KweBoakye/dactyl-manuform-mini-keyboard/parts/caps/DES-kyria-R1T1.stl

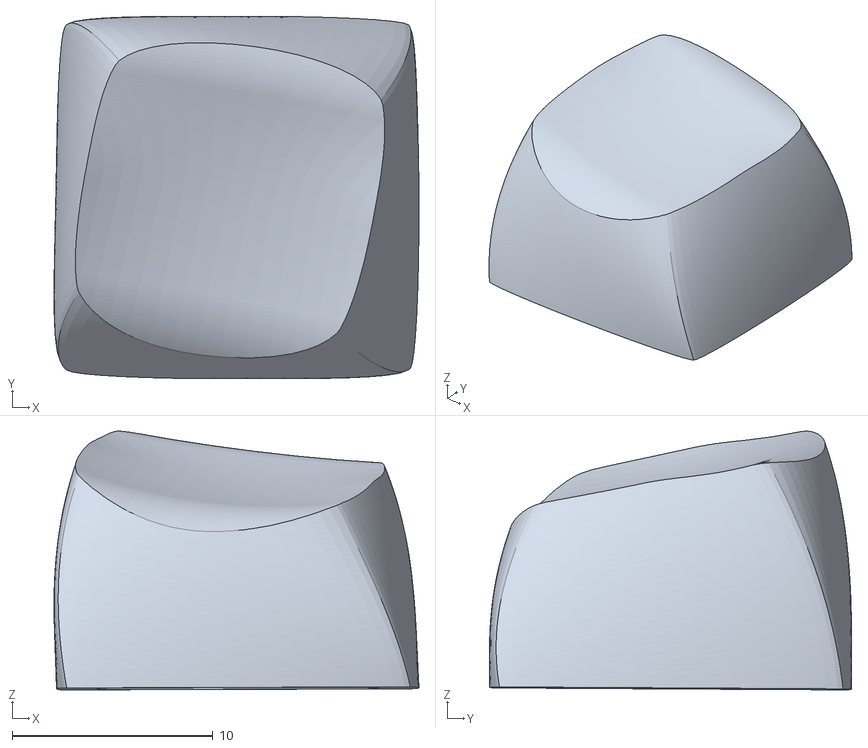
[picture p18: CAD file, 2022-10-28]
parts/caps/DES-kyria-R1T1.stl
18.2 x 18.1 x 12.9
