KweBoakye/dactyl-manuform-mini-keyboard/parts/caps/DES-R4.stl

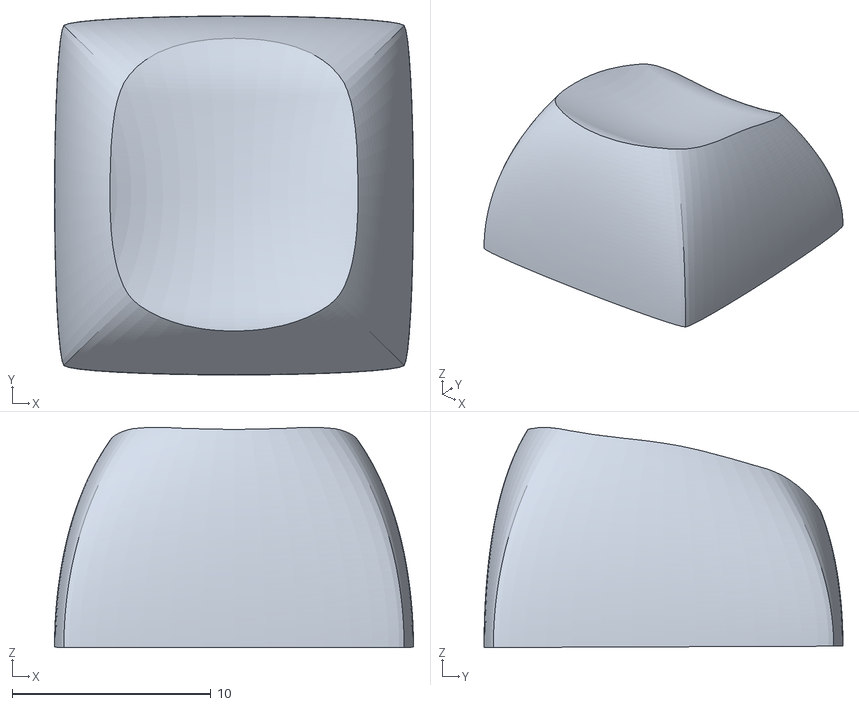
[picture p19: CAD file, 2022-10-28]
parts/caps/DES-R4.stl
18.1 x 18.1 x 11.1
