KweBoakye/dactyl-manuform-mini-keyboard/parts/plate_v4_103.stl

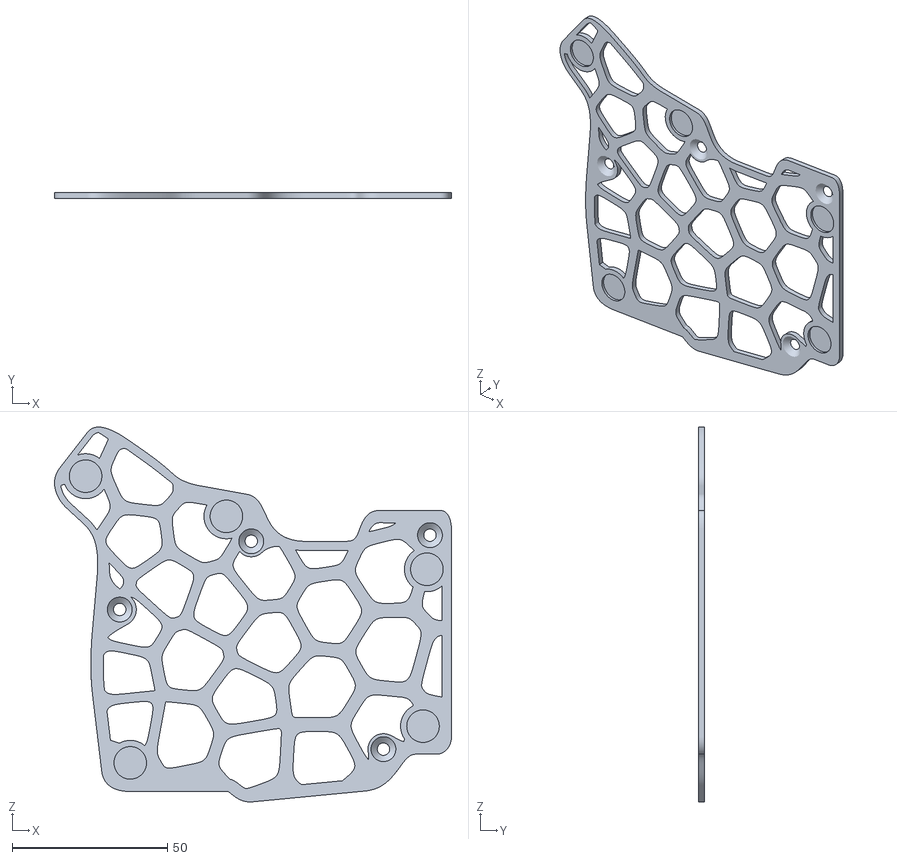
[picture p20: CAD file, 2024-05-14]
parts/plate_v4_103.stl
128.0 x 2.00 x 120.9
