KweBoakye/dactyl-manuform-mini-keyboard/parts/caps/DES-R5.stl

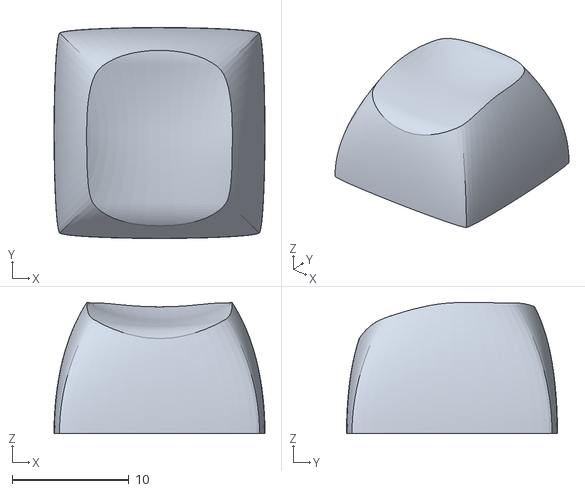
[picture p21: CAD file, 2022-10-28]
parts/caps/DES-R5.stl
18.1 x 18.1 x 11.2
