KweBoakye/dactyl-manuform-mini-keyboard/parts/ImageToStl.com_dt_azc276a02_pcb1_00a.stl

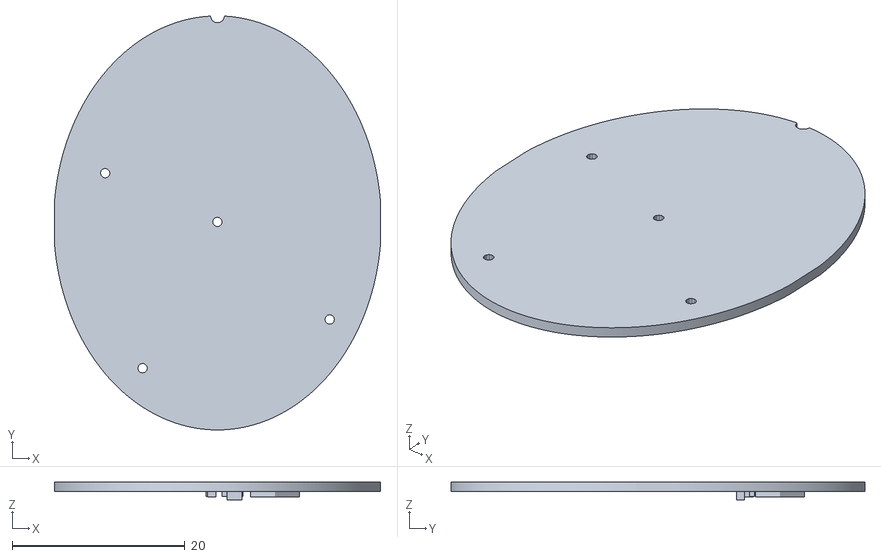
[picture p22: CAD file, 2024-05-14]
parts/ImageToStl.com_dt_azc276a02_pcb1_00a.stl
37.8 x 48.0 x 2.04
