KweBoakye/dactyl-manuform-mini-keyboard/parts/caps/DES-kyria-R1T0.stl

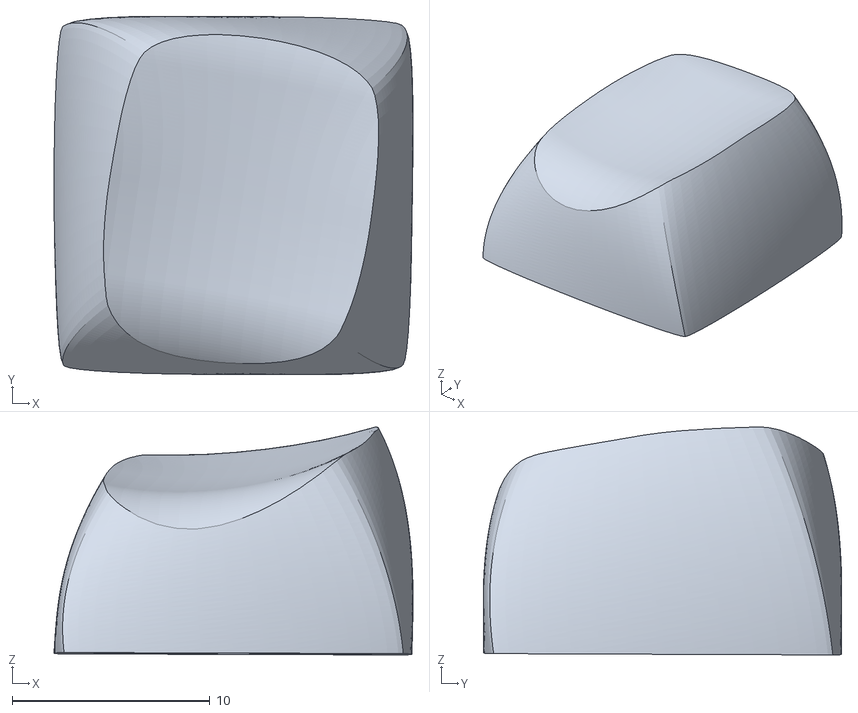
[picture p23: CAD file, 2022-10-28]
parts/caps/DES-kyria-R1T0.stl
18.1 x 18.1 x 11.5
