KweBoakye/dactyl-manuform-mini-keyboard/parts/crkbd-baseplate-magsafe.stl

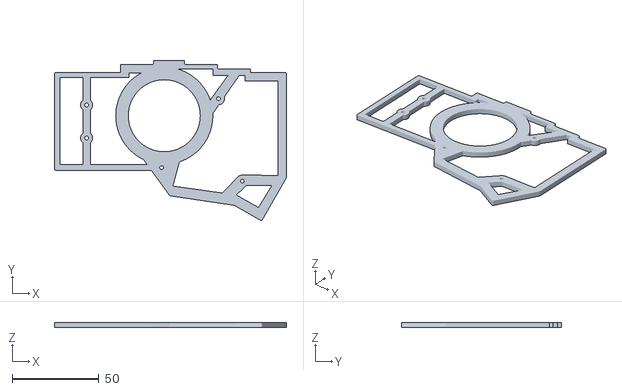
[picture p24: CAD file, 2024-05-14]
parts/crkbd-baseplate-magsafe.stl
133.8 x 92.2 x 3.00
