KweBoakye/dactyl-manuform-mini-keyboard/parts/caps/DES-R3.stl

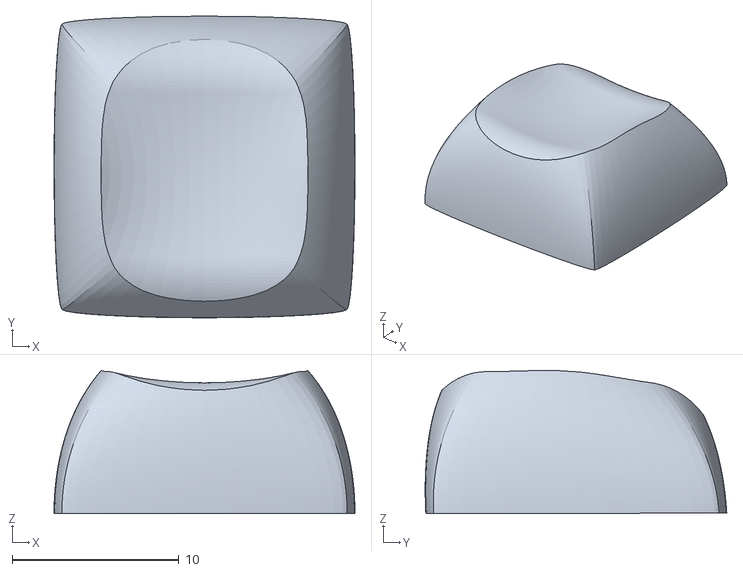
[picture p25: CAD file, 2022-10-28]
parts/caps/DES-R3.stl
18.1 x 18.1 x 8.60
