KweBoakye/dactyl-manuform-mini-keyboard/parts/spi_eeprom_breakout.stl

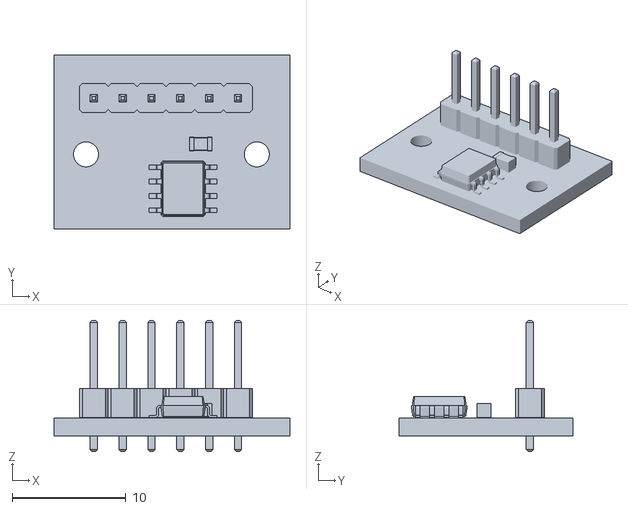
[picture p26: CAD file, 2023-10-07]
parts/spi_eeprom_breakout.stl
20.8 x 15.3 x 11.5
