KweBoakye/dactyl-manuform-mini-keyboard/parts/caps/DES-R2.stl

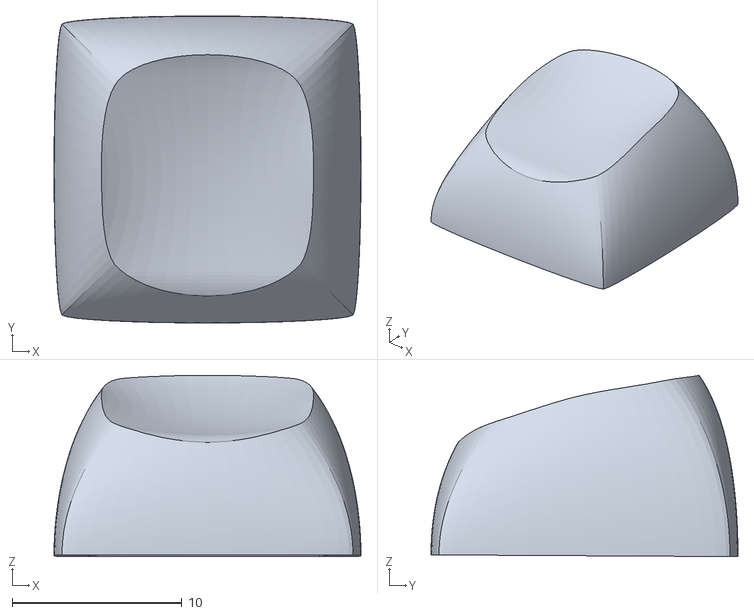
[picture p27: CAD file, 2022-10-28]
parts/caps/DES-R2.stl
18.1 x 18.1 x 10.7
