KweBoakye/dactyl-manuform-mini-keyboard/parts/Tps-65-breakout.stl

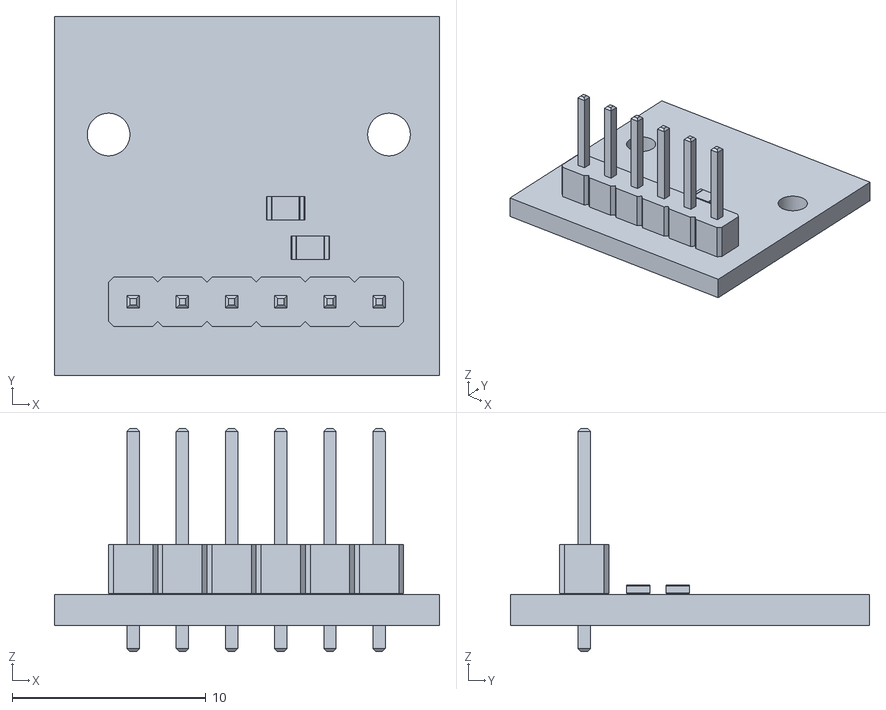
[picture p28: CAD file, 2023-10-07]
parts/Tps-65-breakout.stl
19.9 x 18.5 x 11.5
