KweBoakye/dactyl-manuform-mini-keyboard/parts/caps/DES-R1.stl

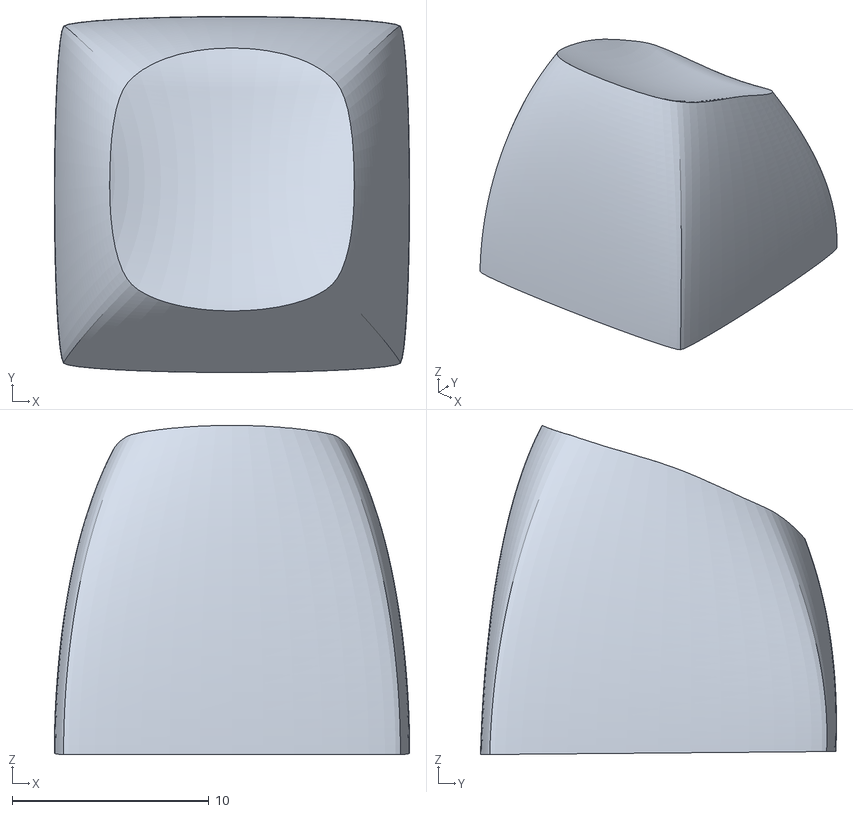
[picture p29: CAD file, 2022-10-28]
parts/caps/DES-R1.stl
18.1 x 18.1 x 16.7
