KweBoakye/dactyl-manuform-mini-keyboard/parts/sk8707-5x-breakout.stl

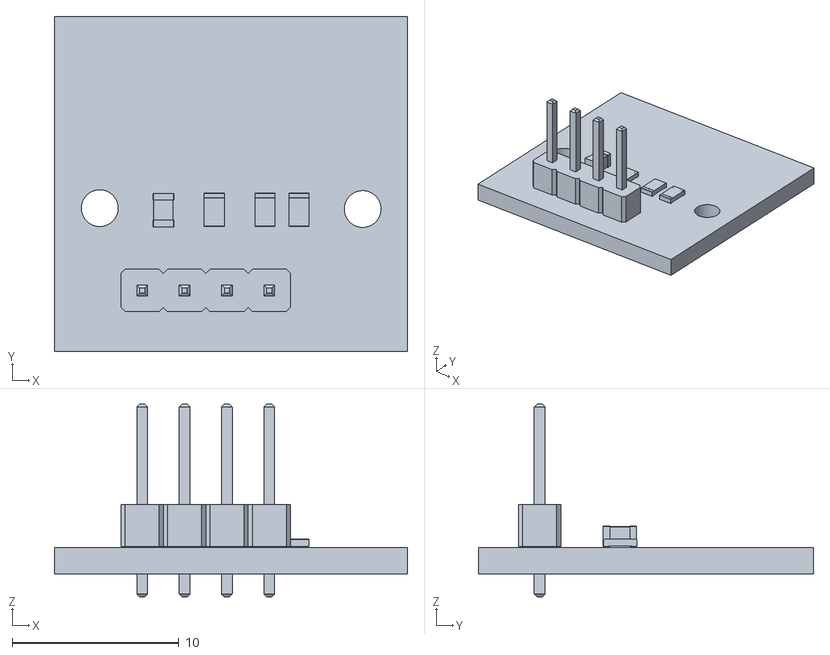
[picture p30: CAD file, 2023-10-07]
parts/sk8707-5x-breakout.stl
21.2 x 20.1 x 11.5
