KweBoakye/dactyl-manuform-mini-keyboard/parts/caps/DES-kyria-R1T3.stl

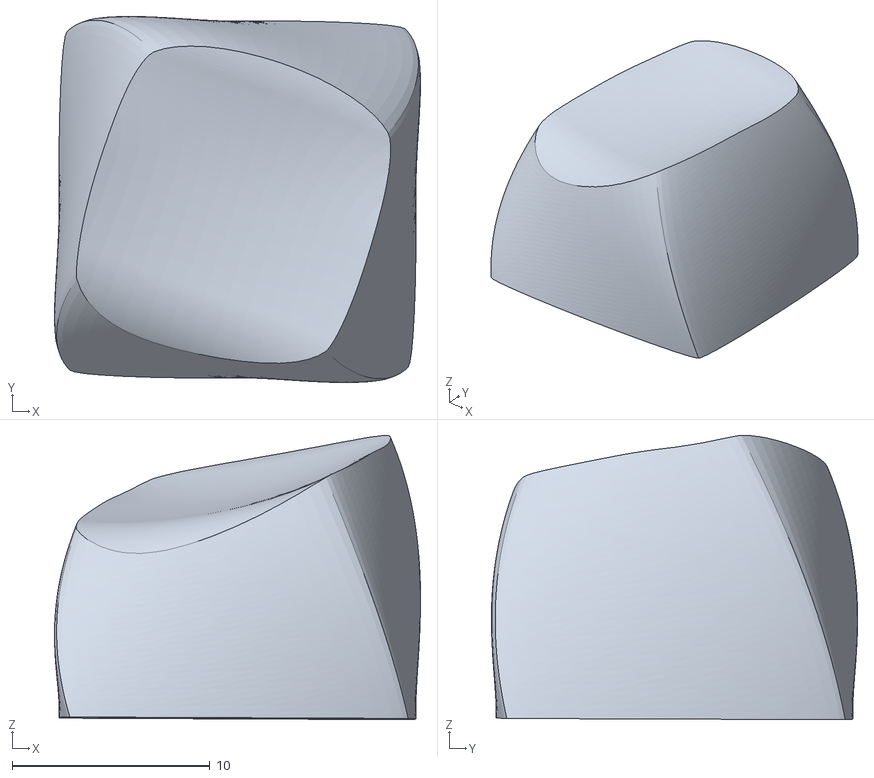
[picture p31: CAD file, 2022-10-28]
parts/caps/DES-kyria-R1T3.stl
18.5 x 18.5 x 14.4
