KweBoakye/dactyl-manuform-mini-keyboard/parts/IS31FL3743x_Breakout.stl

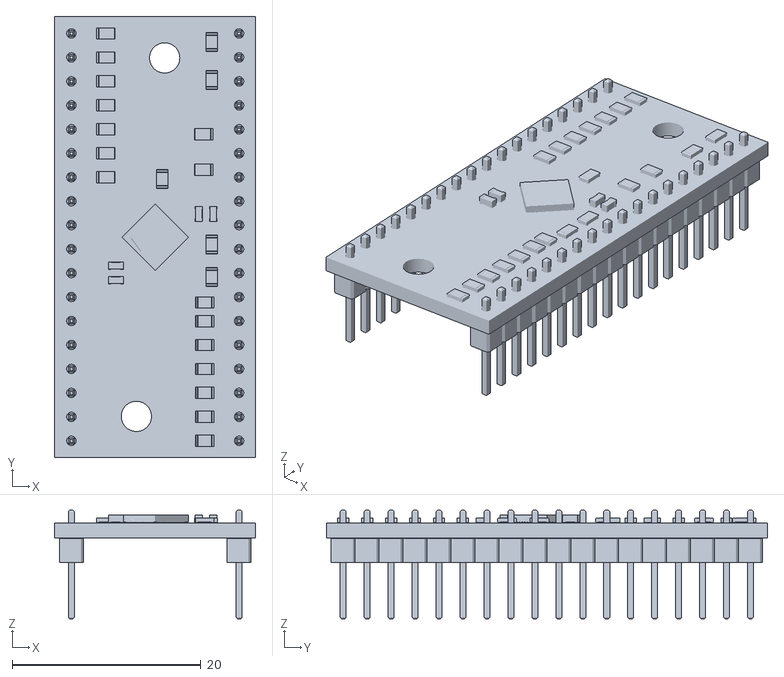
[picture p32: CAD file, 2023-10-07]
parts/IS31FL3743x_Breakout.stl
21.3 x 46.8 x 11.5
