KweBoakye/dactyl-manuform-mini-keyboard/parts/2305 DRV2605L.stl

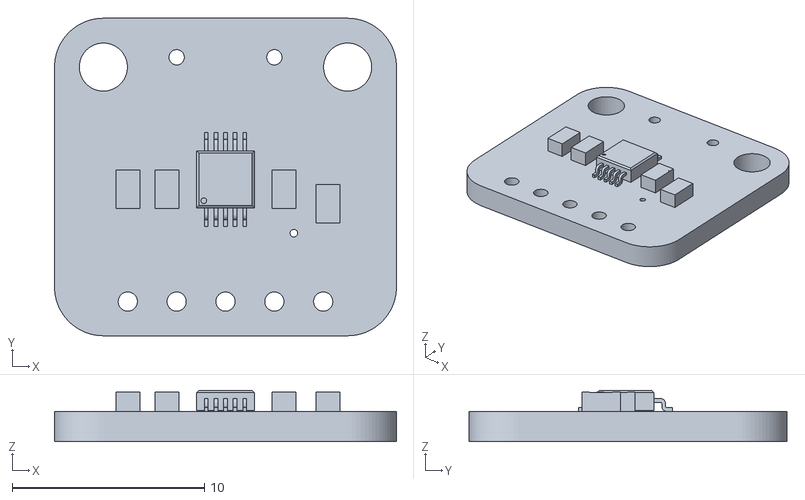
[picture p33: CAD file, 2023-10-07]
parts/2305 DRV2605L.stl
17.8 x 16.5 x 2.67
