KweBoakye/dactyl-manuform-mini-keyboard/parts/tps-43.stl

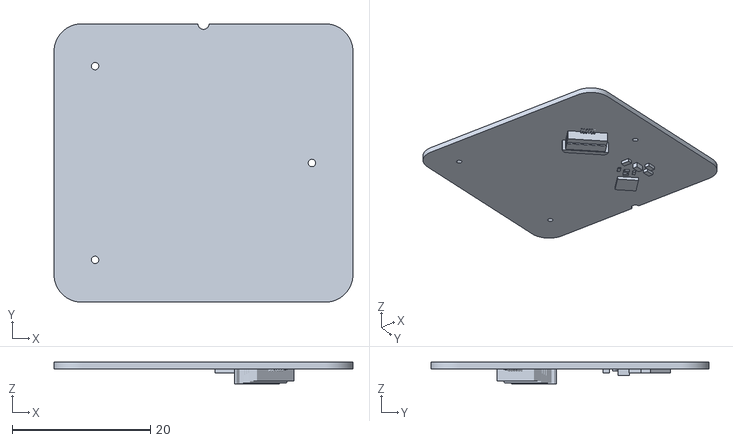
[picture p34: CAD file, 2023-08-23]
parts/tps-43.stl
43.3 x 40.3 x 3.15
