KweBoakye/dactyl-manuform-mini-keyboard/parts/tps-65.stl

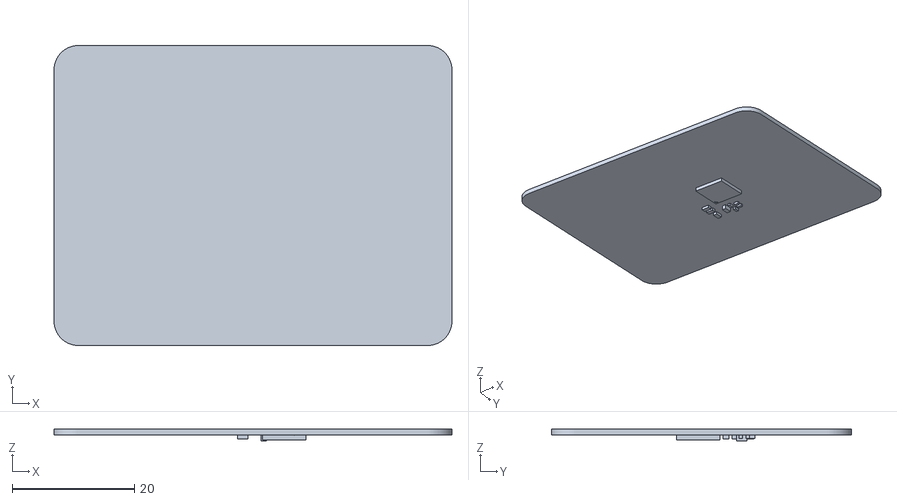
[picture p35: CAD file, 2023-08-23]
parts/tps-65.stl
65.0 x 49.0 x 1.95
