KweBoakye/dactyl-manuform-mini-keyboard/parts/pin header  2.54-12.stl

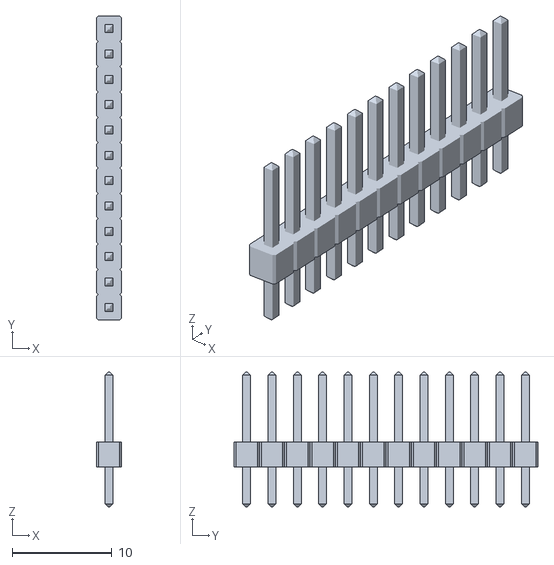
[picture p36: CAD file, 2023-05-24]
parts/pin header 2.54-12.stl
2.54 x 30.5 x 13.5
