KweBoakye/dactyl-manuform-mini-keyboard/parts/adafruit kb2040.stl

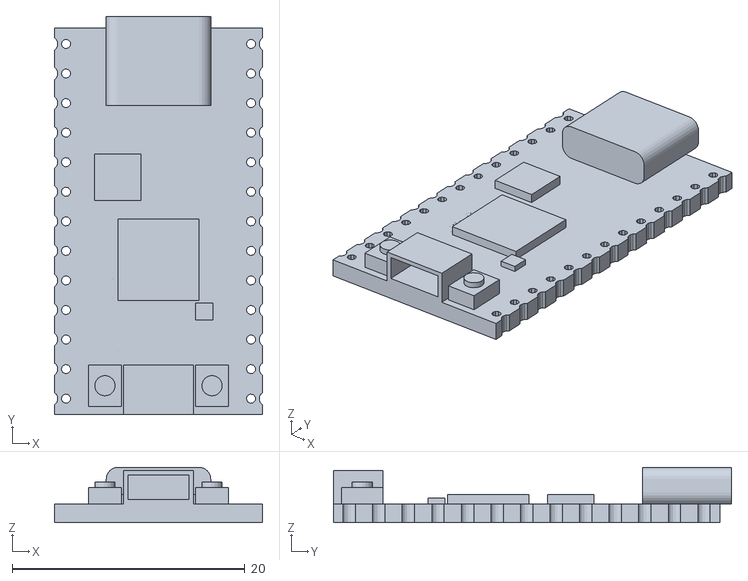
[picture p37: CAD file, 2023-05-24]
parts/adafruit kb2040.stl
17.9 x 34.2 x 4.75
