KweBoakye/dactyl-manuform-mini-keyboard/parts/pim452.stl

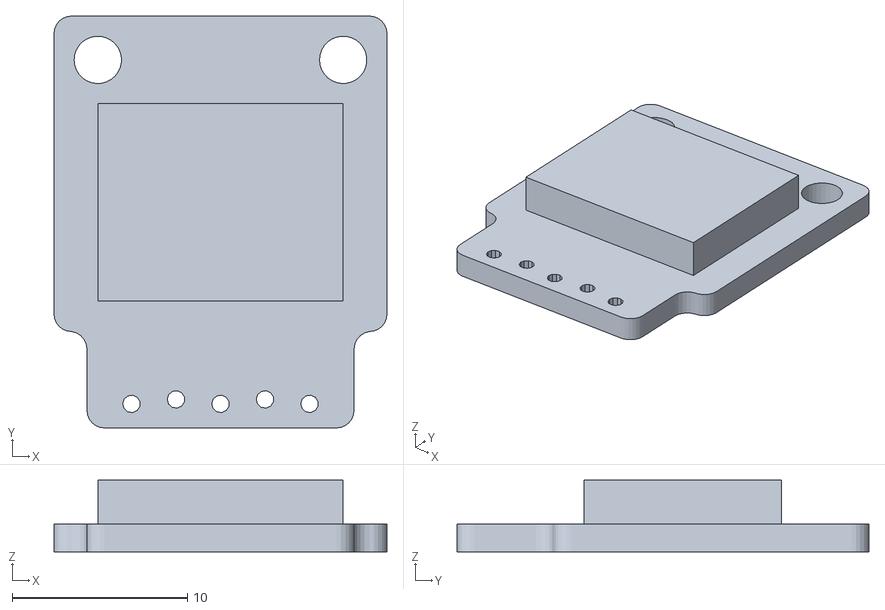
[picture p38: CAD file, 2023-05-24]
parts/pim452.stl
19.0 x 23.5 x 4.10
