KweBoakye/dactyl-manuform-mini-keyboard/parts/pico-r3.stl

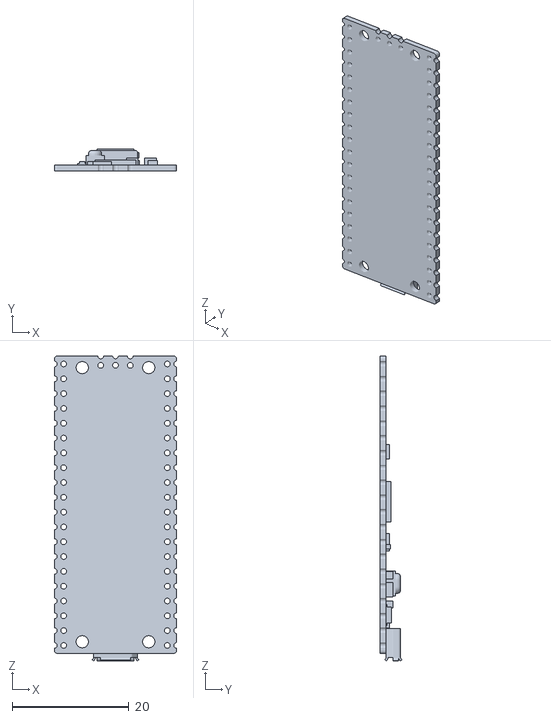
[picture p39: CAD file, 2023-05-17]
parts/pico-r3.stl
21.0 x 3.73 x 52.3
