KweBoakye/dactyl-manuform-mini-keyboard/parts/USB_Type_C_Female_Connector.stl

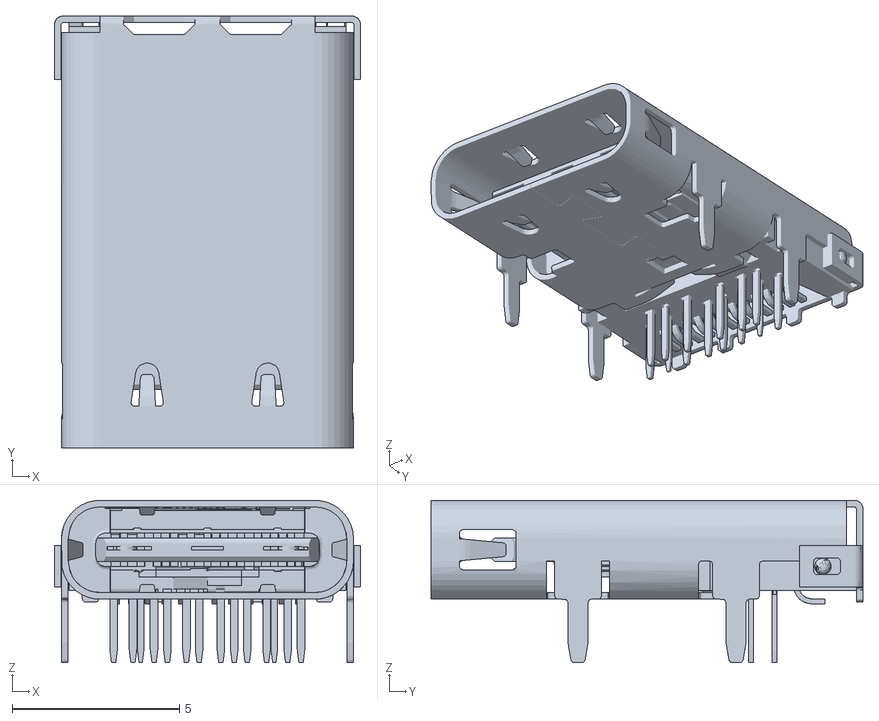
[picture p40: CAD file, 2023-05-17]
parts/USB_Type_C_Female_Connector.stl
9.16 x 12.9 x 4.86
