KweBoakye/dactyl-manuform-mini-keyboard/parts/Kailh LP Choc Burnt Orange.stl

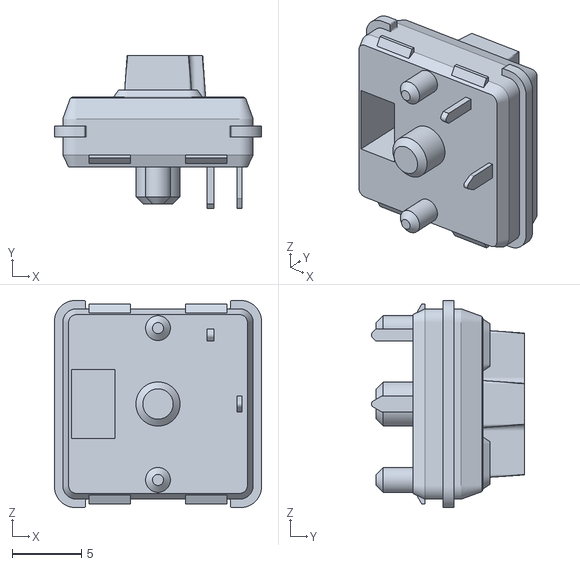
[picture p41: CAD file, 2023-05-17]
parts/Kailh LP Choc Burnt Orange.stl
15.0 x 11.1 x 15.0
