KweBoakye/dactyl-manuform-mini-keyboard/parts/usb connector type c female 6pin.stl

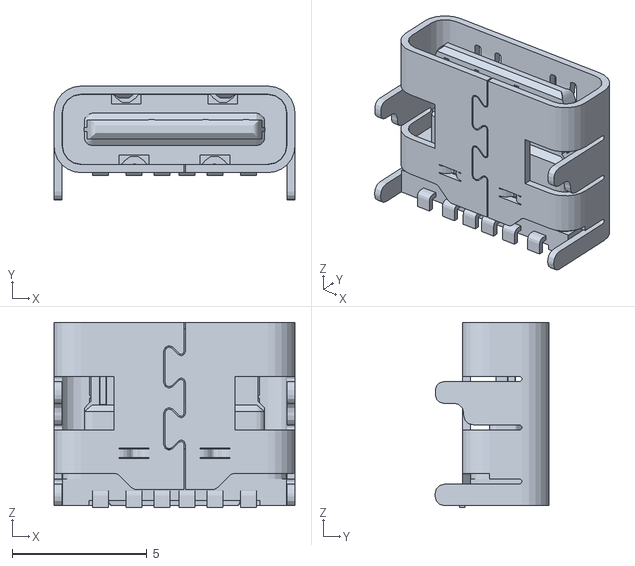
[picture p42: CAD file, 2023-05-17]
parts/usb connector type c female 6pin.stl
8.94 x 4.22 x 6.87
