KweBoakye/dactyl-manuform-mini-keyboard/parts/KLOR_polydactyl_3DP_switchplate.stl

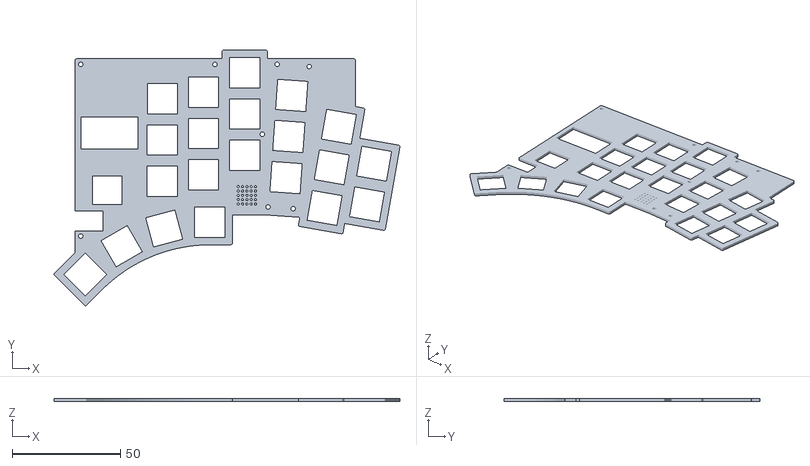
[picture p43: CAD file, 2023-03-25]
parts/KLOR_polydactyl_3DP_switchplate.stl
160.0 x 118.2 x 1.50
