KweBoakye/dactyl-manuform-mini-keyboard/parts/2.54mm x 1 Male Header.stl

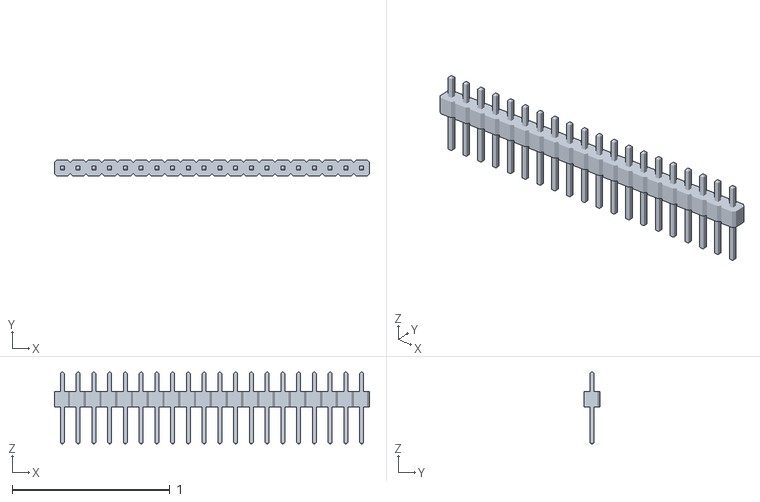
[picture p44: CAD file, 2022-12-14]
parts/2.54mm x 1 Male Header.stl
2.00 x 0.1 x 0.454
