KweBoakye/dactyl-manuform-mini-keyboard/parts/ImageToStl.com_pin header 1x16 th pitch 2.54mm.stl

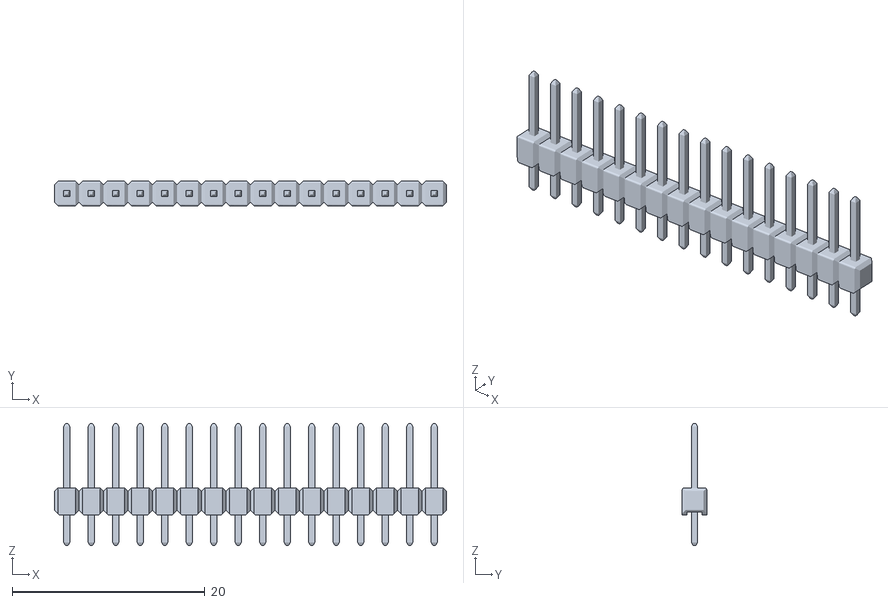
[picture p45: CAD file, 2022-12-14]
parts/ImageToStl.com_pin header 1x16 th pitch 2.54mm.stl
40.6 x 2.54 x 12.7
