KweBoakye/dactyl-manuform-mini-keyboard/parts/Kailh Polia.stl

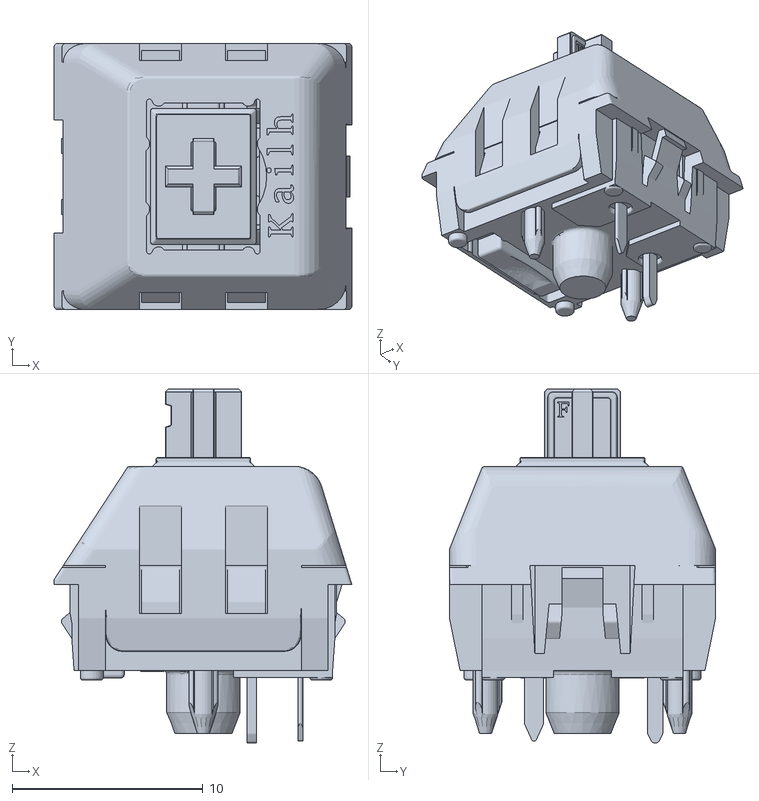
[picture p46: CAD file, 2022-10-28]
parts/Kailh Polia.stl
15.6 x 13.9 x 18.5
