KweBoakye/dactyl-manuform-mini-keyboard/parts/ST7789.stl

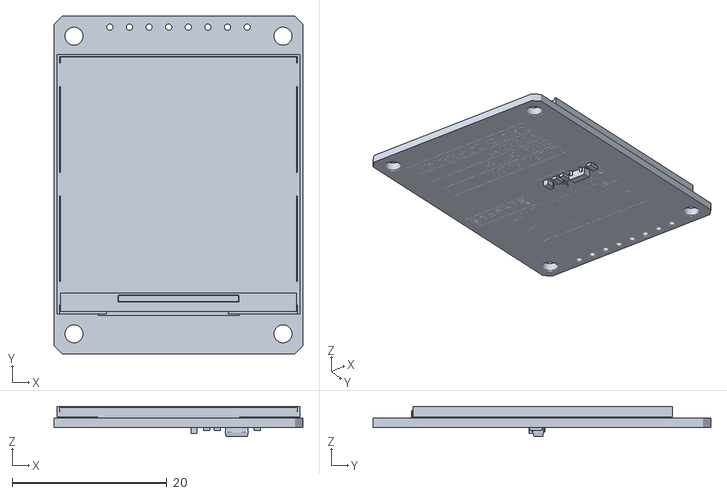
[picture p47: CAD file, 2022-10-28]
parts/ST7789.stl
32.2 x 43.7 x 3.89
