KweBoakye/dactyl-manuform-mini-keyboard/parts/tactileswitch-short.STL

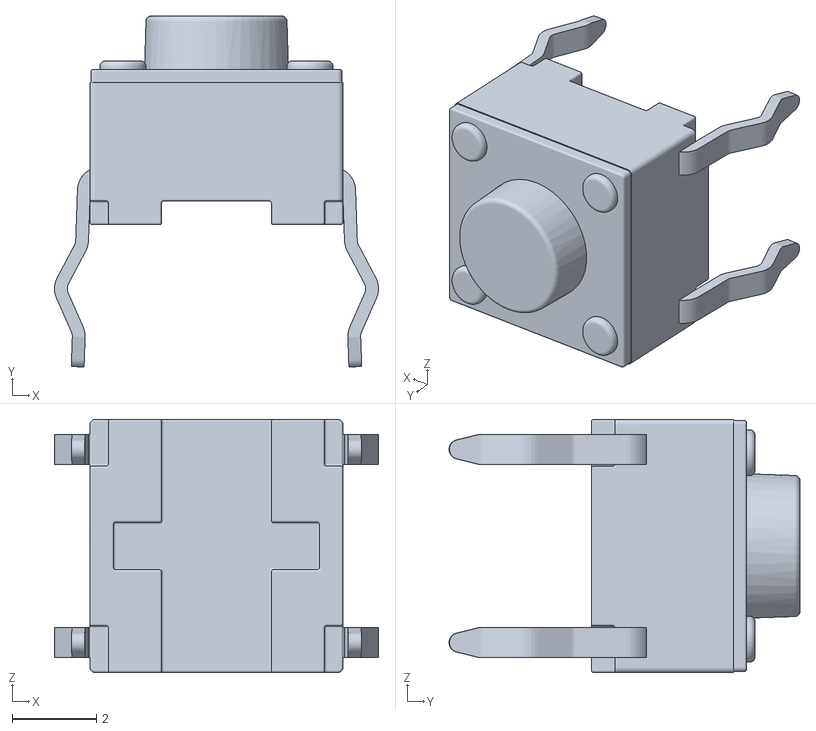
[picture p48: CAD file, 2022-10-28]
parts/tactileswitch-short.STL
7.69 x 8.33 x 6.01
